frntc/Sidekick64/Source/Firmware/kernel_sid.cpp

/*
  _________.__    .___      __   .__        __          _________.___________   
 /   _____/|__| __| _/____ |  | _|__| ____ |  | __     /   _____/|   \______ \  
 \_____  \ |  |/ __ |/ __ \|  |/ /  |/ ___\|  |/ /     \_____  \ |   ||    |  \ 
 /        \|  / /_/ \  ___/|    <|  \  \___|    <      /        \|   ||    `   \
/_______  /|__\____ |\___  >__|_ \__|\___  >__|_ \    /_______  /|___/_______  /
        \/         \/    \/     \/       \/     \/            \/             \/ 
 
 kernel_sid.cpp

 Sidekick64 - A framework for interfacing 8-Bit Commodore computers (C64/C128,C16/Plus4,VC20) and a Raspberry Pi Zero 2 or 3A+/3B+
            - Sidekick SID: a SID and SFX Sound Expander Emulation 
  		      (using reSID by Dag Lem and FMOPL by Jarek Burczynski, Tatsuyuki Satoh, Marco van den Heuvel, and Acho A. Tang)
 Copyright (c) 2019-2022 Carsten Dachsbacher <frenetic@dachsbacher.de>

 Logo created with http://patorjk.com/software/taag/
 
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
 You should have received a copy of the GNU General Public License
 along with this program.  If not, see <http://www.gnu.org/licenses/>.
*/
#include <math.h>
#include "kernel_sid.h"
#ifdef COMPILE_MENU
#include "kernel_menu.h"
#include "launch.h"

static u32 launchPrg;
#endif


//static const char FILENAME_MIDI_SOUNDFONT[] = "SD:MIDI/TimGM6mb.sf2";	// 6 mb
//static const char FILENAME_MIDI_SOUNDFONT[] = "SD:MIDI/Ct4mgm.sf2";	// 4 mb
//static const char FILENAME_MIDI_SOUNDFONT[] = "SD:MIDI/FluidR3_GM.sf2";

static const char FILENAME_SPLASH_RGB[] = "SD:SPLASH/sk64_sid_bg2.tga";
static const char FILENAME_SPLASH_RGB2[] = "SD:SPLASH/sk64_sid_bg.tga";
static const char FILENAME_LED_RGB[] = "SD:SPLASH/sk64_sid_led.tga";

//                 _________.___________         ____                      ________    ______  ____________  
//_______   ____  /   _____/|   \______ \       /  _ \       ___.__. _____ \_____  \  /  __  \/_   \_____  \ 
//\_  __ \_/ __ \ \_____  \ |   ||    |  \      >  _ </\    <   |  |/     \  _(__  <  >      < |   |/  ____/ 
// |  | \/\  ___/ /        \|   ||    `   \    /  <_\ \/     \___  |  Y Y  \/       \/   --   \|   /       \ 
// |__|    \___  >_______  /|___/_______  /    \_____\ \     / ____|__|_|  /______  /\______  /|___\_______ \
//             \/        \/             \/            \/     \/          \/       \/        \/             \/
#include "resid/sid.h"

using namespace reSID;
u32 CLOCKFREQ = 985248;	// exact clock frequency of the C64 will be measured at start up

// SID types and digi boost (only for MOS8580)
unsigned int SID_MODEL[2] = { 8580, 8580 };
unsigned int SID_DigiBoost[2] = { 0, 0 };

// do not change this value
#define NUM_SIDS 2 
SID *sid[ NUM_SIDS ];

#ifdef EMULATE_OPL2
FM_OPL *pOPL;
u32 fmOutRegister;
u16 hack_OPL_Sample_Value[ 2 ];
u8 hack_OPL_Sample_Enabled;
#endif

extern u8 *flash_cacheoptimized_pool;

// a ring buffer storing SID-register writes (filled in FIQ handler)
// TODO should be much smaller
#define RING_SIZE (1024*80)
static u32 *ringBufGPIO;// = (u32*)&flash_cacheoptimized_pool[ 0 ]; //[ RING_SIZE ];
static unsigned long long *ringTime;// = (unsigned long long *)&flash_cacheoptimized_pool[ RING_SIZE * 4 ]; //[ RING_SIZE ];
//static u32 ringBufGPIO[ RING_SIZE ];
//static unsigned long long ringTime[ RING_SIZE ];
static u32 ringWrite;

// prepared GPIO output when SID-registers are read
u32 outRegisters[ 32 ];
u32 outRegisters_2[ 32 ];

u32 fmFakeOutput = 0;
u32 fmAutoDetectStep = 0;
u32 sidFakeOutput = 0;
u32 sidAutoDetectStep = 0;
u32 sidAutoDetectStep_2 = 0;
uint8_t sidAutoDetectRegs[ 32 ];
uint8_t sidAutoDetectRegs_2[ 32 ];

// counts the #cycles when the C64-reset line is pulled down (to detect a reset)
u32 resetCounter,
	cyclesSinceReset,  
	resetPressed, resetReleased;

// Datel MIDI-interface
/*const uint8_t MIDI_CONTROL_REG  = 0x04;
const uint8_t MIDI_STATUS_REG   = 0x06;
const uint8_t MIDI_TRANSMIT_REG = 0x05;
const uint8_t MIDI_RECEIVE_REG  = 0x07;*/

// Sequential MIDI-interface
const uint8_t MIDI_CONTROL_REG  = 0x00;
const uint8_t MIDI_STATUS_REG   = 0x02;
const uint8_t MIDI_TRANSMIT_REG = 0x01;
const uint8_t MIDI_RECEIVE_REG  = 0x03;

// Passport/Sentech MIDI-interface
/*const uint8_t MIDI_CONTROL_REG  = 0x08;
const uint8_t MIDI_STATUS_REG   = 0x08;
const uint8_t MIDI_TRANSMIT_REG = 0x09;
const uint8_t MIDI_RECEIVE_REG  = 0x09;*/

// Datel + Sequential simultaneously
// => address < 8 and (address&3)==sequential

#define SUPPORT_MIDI

#ifdef SUPPORT_MIDI

#define TSF_IMPLEMENTATION
#define TSF_NO_STDIO
#include "tsf.h"

tsf *TinySoundFont = NULL;
#endif

// this is the actual configuration of the emulation
u32 cfgRegisterRead = 0;			// don't use this when you have a SID(-replacement) in the C64
u32 cfgEmulateOPL2 = 1;
u32 cfgSID2_Disabled = 0;
u32 cfgSID2_PlaySameAsSID1 = 0;
u32 cfgMixStereo = 1;
u32 cfgSID2_Addr = 0;
s32 cfgVolSID1_Left, cfgVolSID1_Right;
s32 cfgVolSID2_Left, cfgVolSID2_Right;
s32 cfgVolOPL_Left, cfgVolOPL_Right;
s32 cfgMIDI = 0, cfgSoundFont = 0, cfgMIDIVolume = 0;

extern u32 wireSIDAvailable;

u32 outputPWM = 1, outputHDMI = 0, outputHDMISound = 0;

void setSIDConfiguration( u32 mode, u32 sid1, u32 sid2, u32 sid2addr, u32 rr, u32 addr, u32 exp, s32 v1, s32 p1, s32 v2, s32 p2, s32 v3, s32 p3, s32 outputPWMHDMI, s32 MIDI, s32 soundfont, s32 midiVol )
{
	SID_MODEL[ 0 ] = ( sid1 == 0 ) ? 6581 : 8580;
	SID_DigiBoost[ 0 ] = ( sid1 == 2 ) ? 1 : 0;
	SID_MODEL[ 1 ] = ( sid2 == 0 ) ? 6581 : 8580;
	SID_DigiBoost[ 1 ] = ( sid2 == 2 ) ? 1 : 0;

	// panning = 0 .. 14, vol = 0 .. 15
	// volumes -> 0 .. 255
	cfgVolSID1_Left  = v1 * ( 14 - p1 );
	cfgVolSID1_Right = v1 * ( p1 );
	cfgVolSID2_Left  = v2 * ( 14 - p2 );
	cfgVolSID2_Right = v2 * ( p2 );
	cfgVolOPL_Left  = v3 * ( 14 - p3 );
	cfgVolOPL_Right = v3 * ( p3 );

	if ( outputPWMHDMI == 0 || outputPWMHDMI == 2 )
	{
		int maxVolFactor = max( cfgVolSID1_Left, max( cfgVolSID1_Right, max( cfgVolSID2_Left, max( cfgVolSID2_Right, max( cfgVolOPL_Left, cfgVolOPL_Right ) ) ) ) );

		cfgVolSID1_Left  = cfgVolSID1_Left  * 256 / maxVolFactor;
		cfgVolSID1_Right = cfgVolSID1_Right * 256 / maxVolFactor;
		cfgVolSID2_Left  = cfgVolSID2_Left  * 256 / maxVolFactor;
		cfgVolSID2_Right = cfgVolSID2_Right * 256 / maxVolFactor;
		cfgVolOPL_Left   = cfgVolOPL_Left   * 256 / maxVolFactor;
		cfgVolOPL_Right  = cfgVolOPL_Right  * 256 / maxVolFactor;
	}

	if ( sid2 == 3 ) 
	{ 
		cfgSID2_Disabled = 1; cfgVolSID2_Left = cfgVolSID2_Right = 0;
	} else 
		cfgSID2_Disabled = 0;

	if ( addr == 0 ) cfgSID2_PlaySameAsSID1 = 1; else cfgSID2_PlaySameAsSID1 = 0;
	if ( mode == 0 ) cfgMixStereo = 1; else cfgMixStereo = 0;


	cfgSID2_Addr = sid2addr; // 0 = $d420, 1 = $d500, 2 = $de00
	cfgRegisterRead = rr;
	cfgEmulateOPL2 = exp;

	/*if ( !wireSIDAvailable )
	{
		cfgVolSID1_Left  = 0;
		cfgVolSID1_Right = 0;
		cfgVolSID2_Left  = 0;
		cfgVolSID2_Right = 0;
		cfgSID2_Disabled = 0;
		cfgRegisterRead  = 0;
	}*/

	if ( !exp )
	{
		cfgVolOPL_Left = cfgVolOPL_Right = 0;
	}

	outputPWM = outputHDMI = outputHDMISound = 0;
	#ifdef USE_PWM_DIRECT
	if ( outputPWMHDMI == 0 || outputPWMHDMI == 2 )
		outputPWM = 1;
	#endif
	#ifdef HDMI_SOUND
	if ( outputPWMHDMI == 1 || outputPWMHDMI == 2 )
		outputHDMISound = 1;
	#endif

	cfgMIDI = MIDI;
	cfgSoundFont = soundfont;
	cfgMIDIVolume = midiVol;
}

//  __     __                __      ___                   ___ 
// /__` | |  \     /\  |\ | |  \    |__   |\/|    | |\ | |  |  
// .__/ | |__/    /~~\ | \| |__/    |     |  |    | | \| |  |  
//                                                            
void initSID()
{
	resetCounter = 0;

	for ( int i = 0; i < NUM_SIDS; i++ )
	{
		sid[ i ] = new SID;

		for ( int j = 0; j < 25; j++ )
			sid[ i ]->write( j, 0 );

		if ( SID_MODEL[ i ] == 6581 )
		{
			sid[ i ]->set_chip_model( MOS6581 );
			sid[ i ]->set_voice_mask( 0x07 );
			sid[ i ]->input( 0 );
		} else
		{
			sid[ i ]->set_chip_model( MOS8580 );
			if ( SID_DigiBoost[ i ] == 0 )
			{
				sid[ i ]->set_voice_mask( 0x07 );
				sid[ i ]->input( 0 );
			} else
			{
				sid[ i ]->set_voice_mask( 0x0f );
				sid[ i ]->input( -8192 );
			}
		}

		int SID_passband = 90;
		int SID_gain = 97;
		int SID_filterbias = 1000;

		sid[ i ]->adjust_filter_bias( SID_filterbias / 1000.0f );
		sid[ i ]->set_sampling_parameters( CLOCKFREQ, SAMPLE_FAST, SAMPLERATE, SAMPLERATE * SID_passband / 200.0f, SID_gain / 100.0f );
	}

#ifdef EMULATE_OPL2
	if ( cfgEmulateOPL2 )
	{
		pOPL = ym3812_init( 3579545, SAMPLERATE );
		ym3812_reset_chip( pOPL );
		hack_OPL_Sample_Value[ 0 ] = hack_OPL_Sample_Value[ 1 ] = 0;
		hack_OPL_Sample_Enabled = 0;
		fmFakeOutput = 0;
	}
#endif
	fmFakeOutput =
	fmAutoDetectStep = 0;

	sidFakeOutput =
	sidAutoDetectStep =
	sidAutoDetectStep_2 = 0;

	for ( int i = 0; i < 32; i++ )
		outRegisters[ i ] = outRegisters_2[ i ] = 0;

	outRegisters[ 25 ] = outRegisters_2[ 25 ] = 255;
	outRegisters[ 26 ] = outRegisters_2[ 26 ] = 255;

	for ( int i = 0; i < 20; i++ )
	{
		sidAutoDetectRegs[ i ] = 0;
		sidAutoDetectRegs_2[ i ] = 0;
	}

	// ring buffer init
	ringWrite = 0;
	for ( int i = 0; i < RING_SIZE; i++ )
		ringTime[ i ] = 0;
}


unsigned long long cycleCountC64;


#ifdef COMPILE_MENU
extern CLogger			*logger;
extern CTimer			*pTimer;
extern CScheduler		*pScheduler;
extern CInterruptSystem	*pInterrupt;
extern CScreenDevice	*screen;
CSoundBaseDevice	*m_pSound = NULL;
#else

CLogger				*logger;
CTimer				*pTimer;
CScheduler			*pScheduler;
CInterruptSystem	*pInterrupt;
CScreenDevice		*screen;


boolean CKernel::Initialize( void )
{
	boolean bOK = TRUE;

#ifdef USE_HDMI_VIDEO
	if ( bOK ) bOK = m_Screen.Initialize();

	if ( bOK )
	{
		CDevice *pTarget = m_DeviceNameService.GetDevice( m_Options.GetLogDevice(), FALSE );
		if ( pTarget == 0 )
			pTarget = &m_Screen;

		bOK = m_Logger.Initialize( pTarget );
		logger = &m_Logger;
	}
#endif

	if ( bOK ) bOK = m_Interrupt.Initialize();
	if ( bOK ) bOK = m_Timer.Initialize();


	pTimer = &m_Timer;
	pScheduler = &m_Scheduler;
	pInterrupt = &m_Interrupt;
	screen = &m_Screen;

	return bOK;
}
#endif

void quitSID()
{
	for ( int i = 0; i < NUM_SIDS; i++ )
		delete sid[ i ];

#ifdef SUPPORT_MIDI
	if ( TinySoundFont )
		tsf_close( TinySoundFont );
#endif
}

static u32 renderDone = 0;

static u32 visMode = 0;
static u32 visModeGotoNext = 0;

static float px = 120.0f;
static float dx = 0.0f;
static s32 startRow = 1, endRow = 1;
static float vuValueAvg = 0.01f;
static u32 visUpdate = 1;
static int scopeX = 0;
static u8 scopeValues[ 240 ] = {0};
static u32 nPrevLEDs[3] = {0, 0, 0};
static float ledValueAvg[3] = { 0.01f, 0.01f, 0.01f };

static void initVisualization()
{
	visMode = 0;
	visModeGotoNext = 0;
	px = 120.0f;
	dx = 0.0f;
	startRow = 1; endRow = 1;
	vuValueAvg = 0.01f;
	visUpdate = 1;
	scopeX = 0;
	memset( scopeValues, 0, 256 );
	nPrevLEDs[0] = nPrevLEDs[1] = nPrevLEDs[2] = 0;
	ledValueAvg[0] = ledValueAvg[1] = ledValueAvg[2] = 0.01f;
}

static unsigned char tftBackground2[ 240 * 240 * 2 ];
static unsigned char tftLEDs[ 240 * 240 * 2 ];

static u32 vu_Mode = 0;
static u32 vuMeter[4] = { 0, 0, 0, 0 };
static u32 vu_nLEDs = 0xffff;

static u32 allUsedLEDs = 0;

static int busValue = 0;
static int busValueTTL = 0;
static unsigned long long nCyclesEmulated = 0;
static unsigned long long samplesElapsed = 0;

static u32 resetFromCodeState = 0;
static u32 _playingPSID = 0;

static u32 nBytesRead, stage;


static void prepareOnReset( bool refresh = false )
{
#ifdef SUPPORT_MIDI
	if ( TinySoundFont )
		tsf_reset( TinySoundFont );
#endif

	fmFakeOutput =
	fmAutoDetectStep = 0;

	sidFakeOutput =
	sidAutoDetectStep =
	sidAutoDetectStep_2 = 0;

	for ( int i = 0; i < 20; i++ )
	{
		sidAutoDetectRegs[ i ] = 0;
		sidAutoDetectRegs_2[ i ] = 0;
	}

	if ( launchPrg )
		{disableCart = 0; SETCLR_GPIO( configGAMEEXROMSet | bNMI, configGAMEEXROMClr );} else
		{SETCLR_GPIO( bNMI | bDMA | bGAME | bEXROM, 0 );}

	if ( !refresh )
	{
		CleanDataCache();
		InvalidateDataCache();
		InvalidateInstructionCache();
	}

	for ( u32 i = 0; i < 4; i++ )
	{
		if ( _playingPSID )
		{
			extern unsigned char charset[ 4096 ];
			CACHE_PRELOAD_DATA_CACHE( &charset[ 2048 ], 1024, CACHE_PRELOADL2KEEP );
			FORCE_READ_LINEAR32a( (void*)&charset[ 2048 ], 1024, 8192 );
		}

		if ( launchPrg )
		{
			launchPrepareAndWarmCache();
		}

		// FIQ handler
		CACHE_PRELOAD_INSTRUCTION_CACHE( (void*)&FIQ_HANDLER, 6*1024 );
		FORCE_READ_LINEAR32a( (void*)&FIQ_HANDLER, 6*1024, 32768 );
	}

	resetCounter = cycleCountC64 = nCyclesEmulated = samplesElapsed = 0;
	nBytesRead = 0; stage = 1;
}

//static u32 haltC64 = 0, letgoC64 = 0;
//static u32 SID_not_initialized = 1;


u32 SAMPLERATE_ADJUSTED = SAMPLERATE;
extern u32 nSamplesPrecompute;
u32 trackSampleProgress;


u32 fillSoundBuffer;

#ifdef SUPPORT_MIDI

#define MIDI_BUF_SIZE_BITS	5
const int midiBufferSize = 1 << MIDI_BUF_SIZE_BITS;
static float midiSampleBuffer[ 1 << (MIDI_BUF_SIZE_BITS) ] AAA;
static u32 midiBufferOfs = midiBufferSize;

#endif

static int first = 1;


#ifdef COMPILE_MENU
void KernelSIDFIQHandler( void *pParam );

void KernelSIDRun( CGPIOPinFIQ m_InputPin, CKernelMenu *kernelMenu, const char *FILENAME, bool hasData = false, u8 *prgDataExt = NULL, u32 prgSizeExt = 0, u32 c128PRG = 0, u32 playingPSID = 0 )
#else
void CKernel::Run( void )
#endif
{
startHereAfterReset:
	// initialize ARM cycle counters (for accurate timing)
	initCycleCounter();

	// initialize GPIOs
	gpioInit();
	SET_BANK2_OUTPUT

	// initialize latch and software I2C buffer
	initLatch();

	#ifndef COMPILE_MENU
	int screenType = 0;
	#endif

	if ( screenType == 0 )
		allUsedLEDs = LATCH_LED_ALL;
	if ( screenType == 1 )
		allUsedLEDs = LATCH_LED0to1;
	
	latchSetClearImm( 0, LATCH_RESET | allUsedLEDs | LATCH_ENABLE_KERNAL );
	latchSetClear( 0, LATCH_RESET | allUsedLEDs | LATCH_ENABLE_KERNAL );

	SETCLR_GPIO( bNMI | bDMA | bGAME | bEXROM, 0 );

	#ifdef COMPILE_MENU
	_playingPSID = playingPSID;

	if ( screenType == 0 )
	{
		splashScreen( raspi_sid_splash );
	} else
	if ( screenType == 1 )
	{
		tftLoadBackgroundTGA( DRIVE, FILENAME_SPLASH_RGB, 8 );

		int w, h; 
		extern char FILENAME_LOGO_RGBA[128];
		extern unsigned char tempTGA[ 256 * 256 * 4 ];

		if ( tftLoadTGA( DRIVE, FILENAME_LOGO_RGBA, tempTGA, &w, &h, true ) )
		{
			tftBlendRGBA( tempTGA, tftBackground, 0 );
		}

		tftCopyBackground2Framebuffer();

		u32 c1 = rgb24to16( 166, 250, 128 );
		u32 c2 = rgb24to16( 98, 216, 204 );
		u32 c3 = rgb24to16( 233, 114, 36 );
		char b1[64], b2[64], b3[64];
		int charWidth = 16;
		const char *addr[3] = { "$d420", "$d500", "$de00" };

		sprintf( b1, "%s", SID_MODEL[ 0 ] == 6581 ? "6581":"8580" );

		if ( cfgSID2_Disabled )
			b2[ 0 ] = 0; else
		{
			if ( cfgSID2_PlaySameAsSID1 )
			sprintf( b2, "+%s/$d400", SID_MODEL[ 1 ] == 6581 ? "6581":"8580"); else
			sprintf( b2, "+%s/%s", SID_MODEL[ 1 ] == 6581 ? "6581":"8580", addr[cfgSID2_Addr]);
		}

		if ( cfgEmulateOPL2 )
			sprintf( b3, "+fm" ); else
			b3[ 0 ] = 0;

		int l = strlen( b1 ) + strlen( b2 ) + strlen( b3 );
		if ( l * 16 >= 240 )
			charWidth = 13;
		int sx = max( 0, ( 240 - charWidth * l ) / 2 - 2 );
		tftPrint( b1, sx, 224, c1, charWidth == 16 ? 0 : -3 );	sx += strlen( b1 ) * charWidth;
		tftPrint( b2, sx, 224, c2, charWidth == 16 ? 0 : -3 );	sx += strlen( b2 ) * charWidth;
		tftPrint( b3, sx, 224, c3, charWidth == 16 ? 0 : -3 );

#ifdef SUPPORT_MIDI
		if ( cfgMIDI )
		{
						//01234567890123456789
			sprintf( b1, "midi/$de0X" );
			sx = max( 0, ( 240 - charWidth * 10 ) / 2 - 2 );
			tftPrint( b1, sx, 224-16, c1, charWidth == 16 ? 0 : -3 );	
		}
#endif

		tftInit();
		tftSendFramebuffer16BitImm( tftFrameBuffer );
		tftConvertFrameBuffer12Bit();

		tftClearDirty();
		extern void tftPrepareDirtyUpdates();
		tftPrepareDirtyUpdates();
		tftUse12BitColor();

		memcpy( tftBackground2, tftBackground, 240 * 240 * 2 );
		tftLoadBackgroundTGA( DRIVE, FILENAME_LED_RGB, 8 );
		memcpy( tftLEDs, tftBackground, 240 * 240 * 2 );

		tftLoadBackgroundTGA( DRIVE, FILENAME_SPLASH_RGB2, 8 );

		initVisualization();
	} 
	#endif

	ringBufGPIO = (u32*)&flash_cacheoptimized_pool[ 0 ];
	ringTime = (unsigned long long *)&flash_cacheoptimized_pool[ RING_SIZE * 4 ]; 

	//
	// MIDI
	//
#ifdef SUPPORT_MIDI
	if ( cfgMIDI )
	{
		u32 size;
		cfgMIDI = 0;
		char filename[256];
		sprintf( filename, "SD:MIDI/instrument%02d.sf2", cfgSoundFont );
		if ( getFileSize( logger, DRIVE, filename, &size ) )
		{
			if ( size < 256 * 1024 * 1024 )
			{
				u8 *soundfont = new u8[ size ];

				if ( readFile( logger, DRIVE, filename, soundfont, &size ) )
				{
					TinySoundFont = tsf_load_memory( soundfont, size );
					tsf_set_output( TinySoundFont, TSF_MONO, SAMPLERATE, 0.0f );
					//tsf_set_output( TinySoundFont, TSF_STEREO_INTERLEAVED, SAMPLERATE, 0.0f );
					tsf_set_volume( TinySoundFont, 0.5f * (float)cfgMIDIVolume / 15.0f );
					tsf_set_max_voices( TinySoundFont, 64 );
					tsf_channel_set_bank_preset( TinySoundFont, 9, 128, 0 );
					cfgMIDI = 1;
				}
				delete [] soundfont;

				memset( midiSampleBuffer, 0, midiBufferSize * sizeof( float ) );
			}
		}
	}
#endif

	//
	// initialize sound output (either PWM which is output in the FIQ handler, or via HDMI)
	//
	logger->Write( "", LogNotice, "initialize sound output..." );
	initSoundOutput( &m_pSound, NULL, outputPWM | outputHDMISound, outputHDMI );

	#ifdef COMPILE_MENU
	disableCart = 0;

	if ( FILENAME == NULL && !hasData )
	{
		SETCLR_GPIO( bNMI | bDMA | bGAME | bEXROM, 0 );
		launchPrg = 0;
		disableCart = 1;
	} else
	{
		SETCLR_GPIO( configGAMEEXROMSet | bNMI, configGAMEEXROMClr );
		launchPrg = 1;
		if ( launchGetProgram( FILENAME, hasData, prgDataExt, prgSizeExt ) )
			launchInitLoader( false, c128PRG ); else
			launchPrg = 0;
	}
	#endif

	logger->Write( "", LogNotice, "initialize SIDs..." );
	initSID();
	logger->Write( "", LogNotice, "bla..." );

	// ring buffer init
	ringWrite = 0;
	for ( int i = 0; i < RING_SIZE; i++ )
		ringTime[ i ] = 0;

	//
	// setup FIQ
	//
	resetReleased = 0xff;
	resetFromCodeState = 0;

	logger->Write( "", LogNotice, "setup fiq..." );

	#ifdef COMPILE_MENU
	prepareOnReset();
	m_InputPin.ConnectInterrupt( KernelSIDFIQHandler, kernelMenu );
	#else
	m_InputPin.ConnectInterrupt( this->FIQHandler, this );
	#endif
	m_InputPin.EnableInterrupt( GPIOInterruptOnRisingEdge );

	logger->Write( "", LogNotice, "start emulating..." );
	cycleCountC64 = 0;
	nCyclesEmulated = 0;
	samplesElapsed = 0;

	// how far did we consume the commands in the ring buffer?
	unsigned int ringRead = 0;

	#ifdef COMPILE_MENU
	prepareOnReset( true );
	DELAY(1<<22);
	prepareOnReset( true );
	DELAY(1<<22);
	//startHereAfterReset2:
	cycleCountC64 = 0;
	resetCounter = 0;
	latchSetClear( LATCH_RESET, allUsedLEDs | LATCH_ENABLE_KERNAL );

	nBytesRead = 0; stage = 1;
	u32 cycleCountC64_Stage1 = 0;

	first = 1;
	#ifdef HDMI_SOUND
	//extern CHDMISoundBaseDevice *hdmiSoundDevice;
	//hdmiSoundDevice->Cancel();
	//hdmiSoundDevice->Start();
	#endif

	latchSetClear( LATCH_RESET, 0 );
	if ( launchPrg )
	{
		while ( !disableCart )
		{
			if ( ( ( stage == 1 ) && nBytesRead > 0 ) ||
 				 ( ( stage == 2 ) && nBytesRead < 32 && cycleCountC64 - cycleCountC64_Stage1 > 500000 ) )
			{
				if ( stage == 1 ) 
				{ 
					stage = 2; cycleCountC64_Stage1 = cycleCountC64; 
				} else 
				{
					stage = 0;
					latchSetClear( 0, LATCH_RESET );
					DELAY(1<<20);
					latchSetClear( LATCH_RESET, 0 );
					nBytesRead = 0; stage = 1;
					cycleCountC64 = 0;
				}
			}
		
			#ifdef COMPILE_MENU
			TEST_FOR_JUMP_TO_MAINMENU( cycleCountC64, resetCounter )
			#endif
			asm volatile ("wfi");

			if ( resetFromCodeState == 2 )
			{
				EnableIRQs();
				m_InputPin.DisableInterrupt();
				m_InputPin.DisconnectInterrupt();
				return;		
			}
			
/*			if ( cycleCountC64 > 2000000 )
			{
				cycleCountC64 = 0;
				latchSetClear( 0, LATCH_RESET );
				DELAY(1<<20);
				latchSetClear( LATCH_RESET, 0 );
			}*/
		}
		//latchSetClearImm( LATCH_LED0, 0 );
		if ( _playingPSID )
		{
			extern unsigned char charset[ 4096 ];
			CACHE_PRELOAD_DATA_CACHE( &charset[ 2048 ], 1024, CACHE_PRELOADL2KEEP );
		}
		DELAY(1<<22);
	} 
	#endif

	resetReleased = 0;
	resetCounter = cycleCountC64 = 0;
	nCyclesEmulated = 0;
	samplesElapsed = 0;
	ringRead = ringWrite = 0;

	static u32 hdmiVol = 1;

	fillSoundBuffer = 0;

	// mainloop
	while ( true )
	{
		#ifdef COMPILE_MENU
		//TEST_FOR_JUMP_TO_MAINMENU( cycleCountC64, resetCounter )
		if ( cycleCountC64 > 2000000 && resetCounter > 0 && outputHDMI && m_pSound && hdmiVol == 1 ) {
			#ifdef HDMI_SOUND
			//hdmiSoundDevice->Cancel();
			#endif

			hdmiVol = 0;
		}
		if ( cycleCountC64 > 2000000 && resetCounter > 500000 ) {
			//logger->Write( "", LogNotice, "adjusted sample rate: %u Hz", (u32)SAMPLERATE_ADJUSTED );
			#ifdef HDMI_SOUND
			/*extern CHDMISoundBaseDevice *hdmiSoundDevice;
			if ( outputHDMISound )
				hdmiSoundDevice->Cancel();*/
			#endif
			quitSID();
			EnableIRQs();
			m_InputPin.DisableInterrupt();
			m_InputPin.DisconnectInterrupt();
			return;
		}
		#endif

		if ( resetReleased == 1 )
		{
			//logger->Write( "", LogNotice, "adjusted sample rate: %u Hz", (u32)SAMPLERATE_ADJUSTED );
			quitSID();

			EnableIRQs();
			m_InputPin.DisableInterrupt();
			m_InputPin.DisconnectInterrupt();
			goto startHereAfterReset;
		}

		#ifdef COMPILE_MENU
		//if ( screenType_ == 0 )
		{
			if ( renderDone == 2 )
			{
				if ( !sendFramebufferDone() )
					sendFramebufferNext( 1 );		

				if ( sendFramebufferDone() )
					renderDone = 3;
			}
			if ( bufferEmptyI2C() && renderDone == 1 )
			{
				sendFramebufferStart();
				renderDone = 2;
			}
		}
		#endif

	#ifndef EMULATION_IN_FIQ

		s16 val1, val2;
		s32 valOPL;

		unsigned long long cycleCount = cycleCountC64;
		while ( cycleCount > nCyclesEmulated + 20 ) // TODO should be > nCyclesEmulated + 985240/48000
		{
			CACHE_PRELOAD_INSTRUCTION_CACHE( (void*)&FIQ_HANDLER, 6*1024 );

			CACHE_PRELOADL2STRMW( &smpCur );

			unsigned long long samplesElapsedBefore = samplesElapsed;

			long long cycleNextSampleReady = ( ( unsigned long long )(samplesElapsedBefore+1) * ( unsigned long long )CLOCKFREQ ) / ( unsigned long long )SAMPLERATE_ADJUSTED;
			u32 cyclesToNextSample = cycleNextSampleReady - nCyclesEmulated;

			do { // do SID emulation until time passed to create an additional sample (i.e. there may be several cycles until a sample value is created)
				//u32 cyclesToEmulate = min( 256, cycleCount - nCyclesEmulated );
				u32 cyclesToEmulate = min( 32, cycleCount - nCyclesEmulated );

				if ( cyclesToEmulate > cyclesToNextSample )
					cyclesToEmulate = cyclesToNextSample;

				if ( ringRead != ringWrite )
				{
					int cyclesToNextWrite = (signed long long)ringTime[ ringRead ] - (signed long long)nCyclesEmulated;

					if ( (int)cyclesToEmulate > cyclesToNextWrite && cyclesToNextWrite > 0 )
						cyclesToEmulate = cyclesToNextWrite;
				}
				if ( cyclesToEmulate <= 0 )
					cyclesToEmulate = 1;

				//if ( cyclesToEmulate > 0 )
				{
					sid[ 0 ]->clock( cyclesToEmulate );
					#ifndef SID2_DISABLED
					if ( !cfgSID2_Disabled )
						sid[ 1 ]->clock( cyclesToEmulate );
					#endif

					outRegisters[ 27 ] = sid[ 0 ]->read( 27 );
					outRegisters[ 28 ] = sid[ 0 ]->read( 28 );
					if ( !cfgSID2_Disabled )
					{
						outRegisters_2[ 27 ] = 0;
						outRegisters_2[ 28 ] = 0;
					}

					nCyclesEmulated += cyclesToEmulate;
					cyclesToNextSample -= cyclesToEmulate;
				}


				// apply register updates (we do one-cycle emulation steps, but in case we need to catch up...)
				unsigned int readUpTo = ringWrite;

				if ( ringRead != readUpTo && nCyclesEmulated >= ringTime[ ringRead ] )
				{
      quicklyGetAnotherRegisterWrite:
#ifdef SUPPORT_MIDI
					if ( cfgMIDI && (ringBufGPIO[ ringRead ] & (1<<31)) ) // MIDI
					{
						register u8 MC = ringBufGPIO[ ringRead ] & 255;
						register u8 MD1 = ( ringBufGPIO[ ringRead ] >> 8 ) & 255;
						register u8 MD2 = ( ringBufGPIO[ ringRead ] >> 16 ) & 255;
						register u16 pitch;

						register u8 channel = MC & 0x0f;
						MC &= 0xf0;

						switch ( MC )
						{
						default:
							break;
						case 0x90: // note on
							tsf_channel_note_on( TinySoundFont, channel, MD1, (float)MD2 / 127.0f ); 
							break;
						case 0x80: // note off
							tsf_channel_note_off( TinySoundFont, channel, MD1 ); 
							break;
						case 0xc0: // program change
							tsf_channel_set_presetnumber( TinySoundFont, channel, MD1, ( channel == 9 ) );
							break;
						/*case 0xd0: // pressure change
							break;*/
						case 0xe0: // pitch bend
							pitch = MD1 | ( MD2 << 7 );
							tsf_channel_set_pitchwheel( TinySoundFont, channel, pitch );
							break;
						case 0xb0: // control change
							tsf_channel_midi_control( TinySoundFont, channel, MD1, MD2 );
							break;
						}		
					} else
#endif
					{

						unsigned char A, D;
						decodeGPIO( ringBufGPIO[ ringRead ], &A, &D );

						#ifdef EMULATE_OPL2
						if ( cfgEmulateOPL2 && (ringBufGPIO[ ringRead ] & bIO2) )
						{
							if ( ( ( A & ( 1 << 4 ) ) == 0 ) )
							{
								ym3812_write( pOPL, 0, D ); 
							} else
							{
								ym3812_write( pOPL, 1, D );
								if ( pOPL->address == 1 )
								{
									if ( D == 4 ) // enable digi hack
										hack_OPL_Sample_Enabled = 1;  else
										hack_OPL_Sample_Enabled = 0;
								}
								if ( hack_OPL_Sample_Enabled && ( pOPL->address == 0xa0 || pOPL->address == 0xa1 ) ) // digi hack
									hack_OPL_Sample_Value[ pOPL->address - 0xa0 ] = D; else
									hack_OPL_Sample_Value[ 0 ] = hack_OPL_Sample_Value[ 1 ] = 0;
							}
						} else
						#endif
						//#if !defined(SID2_DISABLED) && !defined(SID2_PLAY_SAME_AS_SID1)
						// TODO: generic masks
						if ( !cfgSID2_Disabled && !cfgSID2_PlaySameAsSID1 && (ringBufGPIO[ ringRead ] & SID2_MASK) )
						{
							sid[ 1 ]->write( A & 31, D );
						} else
						//#endif
						{
							sid[ 0 ]->write( A & 31, D );
							//outRegisters[ A & 31 ] = D;
							//#if !defined(SID2_DISABLED) && defined(SID2_PLAY_SAME_AS_SID1)
							if ( !cfgSID2_Disabled && cfgSID2_PlaySameAsSID1 )
								sid[ 1 ]->write( A & 31, D );
							//#endif
						}
					}
					ringRead++;
					ringRead &= ( RING_SIZE - 1 );

					if ( ringRead != ringWrite )
					{
					  s32 t = ringTime[ ringRead ] - nCyclesEmulated;
					  if ( t <= 0 )
						goto quicklyGetAnotherRegisterWrite;
					} 
				}


//				samplesElapsed = ( ( unsigned long long )nCyclesEmulated * ( unsigned long long )SAMPLERATE ) / ( unsigned long long )CLOCKFREQ;
				samplesElapsed = ( ( unsigned long long )nCyclesEmulated * ( unsigned long long )SAMPLERATE_ADJUSTED ) / ( unsigned long long )CLOCKFREQ;

				if ( nCyclesEmulated >= cycleCount && samplesElapsed == samplesElapsedBefore )
					goto NoSampleGeneratedYet;

			} while ( samplesElapsed == samplesElapsedBefore );

			CACHE_PRELOADL2STRMW( &sampleBuffer[ smpCur ] );
			val1 = sid[ 0 ]->output();
			val2 = 0;
			valOPL = 0;

		#ifndef SID2_DISABLED
			if ( !cfgSID2_Disabled )
				val2 = sid[ 1 ]->output();
		#endif

		#ifdef EMULATE_OPL2
			if ( cfgEmulateOPL2 )
			{
				ym3812_update_one( pOPL, &valOPL, 1 );
				// TODO asynchronous read back is an issue, needs to be fixed
				fmOutRegister = encodeGPIO( ym3812_read( pOPL, 0 ) ); 
			}

			if ( hack_OPL_Sample_Enabled )
		        valOPL = ( hack_OPL_Sample_Value[ 0 ] << 5 ) + ( hack_OPL_Sample_Value[ 1 ] << 5 );
		#endif

			//
			// mixer
			//
			register s32 left, right;

#ifdef SUPPORT_MIDI
			register s32 midiSampleLeft;

			midiSampleLeft = 0;
			if ( cfgMIDI )
			{
				if ( midiBufferOfs >= midiBufferSize )
				{
					tsf_render_float( TinySoundFont, &midiSampleBuffer[0], midiBufferSize, 0 );
					midiBufferOfs = 0;
				} 

				midiSampleLeft = midiSampleBuffer[ midiBufferOfs ] * 32767.0f;
				midiSampleBuffer[ midiBufferOfs ] = 0.0f;
				midiBufferOfs ++;
				midiSampleLeft = max( -31768+2, min( 31767-2, midiSampleLeft ) );
			}
#endif
			if ( nCyclesEmulated < 400000 )
				val1 = val2 = 0;
			// yes, it's 1 byte shifted in the buffer, need to fix
			right = ( val1 * cfgVolSID1_Left  + val2 * cfgVolSID2_Left  + valOPL * cfgVolOPL_Left ) >> 8;
			left  = ( val1 * cfgVolSID1_Right + val2 * cfgVolSID2_Right + valOPL * cfgVolOPL_Right ) >> 8;

#ifdef SUPPORT_MIDI
			right += midiSampleLeft;
			left  += midiSampleLeft;
#endif

/*			if ( fadeVolume < 65536 ) 
			{
				left = ( left * fadeVolume ) >> 16;
				right = ( right * fadeVolume ) >> 16;
				fadeVolume ++;
			}*/

			right = max( -32768+2, min( 32767-2, right ) );
			left  = max( -32768+2, min( 32767-2, left ) );

			if ( outputPWM ) 
				putSample( left, right );

			if ( outputHDMISound )
				putSampleHDMI( left << 8, right << 8 );

		#if 1
			// vu meter
			static u32 vu_nValues = 0;
			static float vu_Sum[ 4 ] = { 0.0f, 0.0f, 0.0f, 0.0f };
			
			//if ( vu_Mode != 2 )
			{
				float t = (left+right) / (float)32768.0f * 0.5f;
				vu_Sum[ 0 ] += t * t * 1.0f;

				vu_Sum[ 1 ] += val1 * val1 / (float)32768.0f / (float)32768.0f;
				vu_Sum[ 2 ] += val2 * val2 / (float)32768.0f / (float)32768.0f;
				vu_Sum[ 3 ] += valOPL * valOPL / (float)32768.0f / (float)32768.0f;

				if ( ++ vu_nValues == 256*2 )
				{
					for ( u32 i = 0; i < 4; i++ )
					{
						float vu_Volume = max( 0.0f, 2.0f * (log10( 0.1f + sqrt( (float)vu_Sum[ i ] / (float)vu_nValues ) ) + 1.0f) );
						u32 v = vu_Volume * 1024.0f;
						if ( i == 0 )
						{
							// moving average
							float v = min( 1.0f, (float)vuMeter[ 0 ] / 1024.0f );
							static float led4Avg = 0.0f;
							led4Avg = led4Avg * 0.8f + v * ( 1.0f - 0.8f );

							vu_nLEDs = max( 0, min( 4, (led4Avg * 8.0f) ) );
							if ( vu_nLEDs > 4 ) vu_nLEDs = 4;
						}
						vuMeter[ i ] = v;
						vu_Sum[ i ] = 0;
					}

					vu_nValues = 0;
				}
			}

			#ifdef COMPILE_MENU
			if ( screenType == 0 )
			{
				#include "oscilloscope_hack.h"
			} else
			if ( screenType == 1 )
			{
				const float scaleVis = 1.0f;
				const u32 nLevelMeters = 3;
				#include "tft_sid_vis.h"
			} 
			#endif
		#endif
		NoSampleGeneratedYet:;
		}
	#endif
	}

	m_InputPin.DisableInterrupt();
}


// taken from Circle itself for inlining

#define REG(name, base, offset, base4, offset4)	\
			static const u32 Reg##name = (base) + (offset);
#define REGBIT(reg, name, bitnr)	static const u32 Bit##reg##name = 1U << (bitnr);

REG (MaiData, ARM_HD_BASE, 0x20, ARM_HD_BASE, 0x1C);
REG (MaiControl, ARM_HD_BASE, 0x14, ARM_HD_BASE, 0x10);
	REGBIT (MaiControl, Full, 11);

unsigned m_nSubFrame = 0;
	
const u8 IEC958Table[ 5 ] = 
{
	0b100,	// consumer, PCM, no copyright, no pre-emphasis
	0,	// category (general mode)
	0,	// source number, take no account of channel number
	2,	// sampling frequency 48khz
	0b1011 | (13 << 4) // 24 bit samples, original freq.
};

__attribute__( ( always_inline ) ) inline u32 ConvertIEC958Sample( u32 nSample, unsigned nFrame )
{
	nSample &= 0xFFFFFF;
	nSample <<= 4;

	if ( nFrame < IEC958_STATUS_BYTES * 8 && (IEC958Table[nFrame / 8] & BIT(nFrame % 8)) )
		nSample |= 0x40000000;

	if (__builtin_parity(nSample))
		nSample |= 0x80000000;

	if (nFrame == 0)
		nSample |= IEC958_B_FRAME_PREAMBLE;

	return nSample;
}


#ifdef COMPILE_MENU
void KernelSIDLaunchFIQHandler( void *pParam )
{
	if ( !disableCart )
	{
		register u32 D;

		// after this call we have some time (until signals are valid, multiplexers have switched, the RPi can/should read again)
		START_AND_READ_ADDR0to7_RW_RESET_CS

		// update some counters
		UPDATE_COUNTERS_MIN( cycleCountC64, resetCounter )

		// read the rest of the signals
		WAIT_AND_READ_ADDR8to12_ROMLH_IO12_BA

		LAUNCH_FIQ( resetCounter )
	}
}

void KernelSIDFIQHandler( void *pParam )
#else
void CKernel::FIQHandler (void *pParam)
#endif
{
	register u32 D = 0;

	#ifdef COMPILE_MENU
	if ( launchPrg && !disableCart )
	{
		register u32 D;

		CACHE_PRELOADL2STRM( &prgData[ currentOfs ] );

		// after this call we have some time (until signals are valid, multiplexers have switched, the RPi can/should read again)
		START_AND_READ_ADDR0to7_RW_RESET_CS

		// update some counters
		UPDATE_COUNTERS_MIN( cycleCountC64, resetCounter )

		// read the rest of the signals
		WAIT_AND_READ_ADDR8to12_ROMLH_IO12_BA

		if ( CPU_READS_FROM_BUS && ROML_ACCESS )
			nBytesRead++;

		LAUNCH_FIQ( resetCounter )
	}
	#endif
	static s32 latchDelayOut = 10;

	START_AND_READ_ADDR0to7_RW_RESET_CS

	cycleCountC64 ++;

	if ( CPU_RESET && !resetReleased ) {
		resetPressed = 1; resetCounter ++;
	} else {
		if ( resetPressed && resetCounter > 100 )	
		{
			resetReleased = 1;
			disableCart = transferStarted = 0;
			nBytesRead = 0; stage = 1;
			SETCLR_GPIO( configGAMEEXROMSet | bNMI, configGAMEEXROMClr );
			FINISH_BUS_HANDLING
			return;
		}
		resetPressed = 0;
	}

	#ifdef COMPILE_MENU
	// preload cache
	if ( !( launchPrg && !disableCart ) )
	{
		CACHE_PRELOADL1STRMW( &ringWrite );
		CACHE_PRELOADL1STRM( &sampleBuffer[ smpLast ] );
		CACHE_PRELOADL1STRM( &outRegisters[ 16 ] );
	}
	#endif

	WAIT_AND_READ_ADDR8to12_ROMLH_IO12_BA

	if ( busValueTTL < 0 )
	{
		busValue = 0;  
	} else
		busValueTTL --;

	if ( CPU_WRITES_TO_BUS )
		READ_D0to7_FROM_BUS( D )

	//  __   ___       __      __     __  
	// |__) |__   /\  |  \    /__` | |  \ 
	// |  \ |___ /~~\ |__/    .__/ | |__/ 
	//
	if ( cfgRegisterRead && CPU_READS_FROM_BUS && SID_ACCESS )
	{
		u32 A = ( g2 >> A0 );
		u32 D;// = outRegisters[ A ];

		A |= ( (GET_ADDRESS8to12) & 1 ) << 8;

		if ( !cfgSID2_Disabled &&
			 ( ( cfgSID2_Addr == 0 && (A & 0x20) ) || ( cfgSID2_Addr == 1 && (A & 0x100) ) ) )
		{
			A &= 31;
			if ( sidAutoDetectStep_2 == 1 && A == 0x1b )
			{
				sidAutoDetectStep_2 = 0;
				if ( SID_MODEL[ 1 ] == 8580 )
					D = 2; else
					D = 3;
			} else
			{
				if ( A >= 0x19 && A <= 0x1c )
					D = outRegisters_2[ A & 31 ]; else
					D = busValue;
			}
		} else
		{
			A &= 31;
			if ( sidAutoDetectStep == 1 && A == 0x1b )
			{
				sidAutoDetectStep = 0;
				if ( SID_MODEL[ 0 ] == 8580 )
					D = 2; else
					D = 3;
			} else
			{
				if ( A >= 0x19 && A <= 0x1c )
					D = outRegisters[ A ]; else
					D = busValue;
			}
		}

		WRITE_D0to7_TO_BUS( D )

		FINISH_BUS_HANDLING
		return;
	} 
	if ( _playingPSID && IO2_ACCESS )
	{
		if ( CPU_READS_FROM_BUS && GET_IO12_ADDRESS == 0x55 )
		{
			static u32 oc = 0;
			static u8 nextCharByte = 0;
			WRITE_D0to7_TO_BUS( nextCharByte )
			extern unsigned char charset[ 4096 ];
			oc ++; oc &= 1023;
			nextCharByte = charset[ 2048 + oc ];
			FINISH_BUS_HANDLING
			return;
		}
		if ( resetFromCodeState == 0 && CPU_WRITES_TO_BUS && GET_IO12_ADDRESS == 0x11 )
		{
			//READ_D0to7_FROM_BUS( D )
			if ( D == 0x22 )
				resetFromCodeState = 1;
			OUTPUT_LATCH_AND_FINISH_BUS_HANDLING
			return;
		}
		if ( resetFromCodeState == 1 && CPU_WRITES_TO_BUS && GET_IO12_ADDRESS == 0x33 )
		{
			//READ_D0to7_FROM_BUS( D )
			if ( D == 0x44 )
			{
				resetFromCodeState = 2;
				cfgVolSID1_Left = cfgVolSID2_Left = cfgVolOPL_Left =
				cfgVolSID1_Right = cfgVolSID2_Right = cfgVolOPL_Right = 0;
				latchSetClear( 0, LATCH_RESET );
			}
			OUTPUT_LATCH_AND_FINISH_BUS_HANDLING
			return;
		}
	} 
	//  __   ___       __      ___       
	// |__) |__   /\  |  \    |__   |\/| 
	// |  \ |___ /~~\ |__/    |     |  | 
	//                                   
	#ifdef EMULATE_OPL2
	if ( cfgEmulateOPL2 )
	{
		if ( ( CPU_READS_FROM_BUS && IO2_ACCESS ) && ( GET_IO12_ADDRESS == 0x60 ) )
		{
			//
			// this is not a real read of the YM3812 status register!
			// only a fake that let's the detection routine be satisfied
			//
			u32 D = fmFakeOutput; 
			fmFakeOutput = 0xc0 - fmFakeOutput;

			WRITE_D0to7_TO_BUS( D )

			FINISH_BUS_HANDLING
			return;
		} else
		// reading of the external Sound Expander Keyboard => we don't have it, return 0xFF
		if ( ( CPU_READS_FROM_BUS && IO2_ACCESS ) && ( GET_IO12_ADDRESS >= 0x08 ) && ( GET_IO12_ADDRESS <= 0x0F ) )
		{
			WRITE_D0to7_TO_BUS( 0xFF )

			FINISH_BUS_HANDLING
			return;
		} else
		//       __    ___  ___     ___       
		// |  | |__) |  |  |__     |__   |\/| 
		// |/\| |  \ |  |  |___    |     |  | 
		//                                    
		if ( CPU_WRITES_TO_BUS && IO2_ACCESS ) 
		{
			//READ_D0to7_FROM_BUS( D )

			// this is mimicing some behaviour of the YM let it be detected
			u32 A = ( ( g2 & A_FLAG ) >> A0 ) & ( 1 << 4 ); // A == 0 -> address register, otherwise data register
			
			if ( A == 0 && D == 0x04 && fmAutoDetectStep != 2 )
				fmAutoDetectStep = 1;
			if ( A > 0 && D == 0x60 && fmAutoDetectStep == 1 )
				fmAutoDetectStep = 2;
			if ( A == 0 && D == 0x04 && fmAutoDetectStep == 2 )
				fmAutoDetectStep = 3;
			if ( A > 0 && D == 0x80 && fmAutoDetectStep == 3 )
			{
				fmAutoDetectStep = 4;
				fmFakeOutput = 0;
			}
				
			ringBufGPIO[ ringWrite ] = ( g2 & A_FLAG ) | ( D << D0 ) | bIO2;
			ringTime[ ringWrite ] = cycleCountC64;
			ringWrite ++;
			ringWrite &= ( RING_SIZE - 1 );

			FINISH_BUS_HANDLING
			return;
		} 
	} 
	#endif // EMULATE_OPL2
	//       __    ___  ___     __     __  
	// |  | |__) |  |  |__     /__` | |  \ 
	// |/\| |  \ |  |  |___    .__/ | |__/ 
	//                                   
	if ( CPU_WRITES_TO_BUS && SID_ACCESS ) 
	{
		//READ_D0to7_FROM_BUS( D )

		register u32 A = GET_ADDRESS0to7;
		register u32 remapAddr = (A&31) << A0;

		A |= ( (GET_ADDRESS8to12) & 1 ) << 8;

		if ( ( cfgSID2_Addr == 0 && (A & 0x20) ) ||
			 ( cfgSID2_Addr == 1 && (A & 0x100) ) )
		{
			remapAddr |= SID2_MASK;
			if ( sidAutoDetectStep_2 == 0 &&
				 sidAutoDetectRegs_2[ 0x12 ] == 0xff &&
				 sidAutoDetectRegs_2[ 0x0e ] == 0xff &&
				 sidAutoDetectRegs_2[ 0x0f ] == 0xff &&
				 (A&31) == 0x12 && D == 0x20 )
			{
				sidAutoDetectStep_2 = 1;
			}
			sidAutoDetectRegs_2[ A & 31 ] = D;
		} else
		{
			if ( sidAutoDetectStep == 0 &&
				 sidAutoDetectRegs[ 0x12 ] == 0xff &&
				 sidAutoDetectRegs[ 0x0e ] == 0xff &&
				 sidAutoDetectRegs[ 0x0f ] == 0xff &&
				 (A&31) == 0x12 && D == 0x20 )
			{
				sidAutoDetectStep = 1;
			}
			sidAutoDetectRegs[ A & 31 ] = D;
		}


		busValue = D;
		if ( SID_MODEL[ 0 ] == 8580 )
			busValueTTL = 0xa2000; else // 8580
			busValueTTL = 0x1d00; // 6581

		ringBufGPIO[ ringWrite ] = ( remapAddr | ( D << D0 ) ) & ~bIO2;
		ringTime[ ringWrite ] = cycleCountC64;
		ringWrite ++;
		ringWrite &= ( RING_SIZE - 1 );
		
		FINISH_BUS_HANDLING
		return;
	}
	if ( CPU_WRITES_TO_BUS && IO1_ACCESS && cfgSID2_Addr == 2 ) 
	{
		//READ_D0to7_FROM_BUS( D )

		register u32 A = GET_ADDRESS0to7;
		register u32 remapAddr = ( (A&31) << A0 ) | SID2_MASK;

		ringBufGPIO[ ringWrite ] = ( remapAddr | ( D << D0 ) ) & ~bIO2;
		ringTime[ ringWrite ] = cycleCountC64;
		ringWrite ++;
		ringWrite &= ( RING_SIZE - 1 );

		FINISH_BUS_HANDLING
		return;
	}

	// MIDI experimental support
#ifdef SUPPORT_MIDI
	static uint8_t midiFIFO[ 4 ], midiFIFOIdx = 0;
	if ( cfgMIDI && IO1_ACCESS ) 
	{
		register u32 A = GET_ADDRESS0to7;
		register u8 MC, MD1, MD2;

		if ( A < 8 )
		{
			if ( CPU_WRITES_TO_BUS && (A&3) == MIDI_TRANSMIT_REG )
			{
				midiFIFO[ midiFIFOIdx++ ] = D;
				midiFIFOIdx &= 3;
				MC = midiFIFO[ ( 4 + midiFIFOIdx - 2 ) & 3 ] & 0xf0;
				if ( MC == 0xc0 /*|| MD == 0xd0*/) // program and channel pressure
				{
					MC = midiFIFO[ ( 4 + midiFIFOIdx - 2 ) & 3 ];
					MD1 = midiFIFO[ ( midiFIFOIdx + 4 - 1 ) & 3 ] & 127;
					MD2 = 0;
					ringBufGPIO[ ringWrite ] = (1<<31) | MC | ( MD1 << 8 ) | ( MD2 << 16 );
					ringTime[ ringWrite ] = cycleCountC64;
					ringWrite ++;
					ringWrite &= ( RING_SIZE - 1 );

					*(u32*)&midiFIFO[0] = 0;
				} else
				if ( MC == 0xd0 ) // channel pressure
				{
					*(u32*)&midiFIFO[0] = 0;
				} else
				{
					MC = midiFIFO[ ( 4 + midiFIFOIdx - 3 ) & 3 ] & 0xf0;
					if ( MC == 0x90 || MC == 0x80 || MC == 0xe0 || MC == 0xb0 ) // commands with two parameters
					{
						MC = midiFIFO[ ( 4 + midiFIFOIdx - 3 ) & 3 ];
						MD1 = midiFIFO[ ( midiFIFOIdx + 4 - 2 ) & 3 ] & 127;
						MD2 = midiFIFO[ ( midiFIFOIdx + 4 - 1 ) & 3 ] & 127;
						ringBufGPIO[ ringWrite ] = (1<<31) | MC | ( MD1 << 8 ) | ( MD2 << 16 );
						ringTime[ ringWrite ] = cycleCountC64;
						ringWrite ++;
						ringWrite &= ( RING_SIZE - 1 );
						*(u32*)&midiFIFO[0] = 0;
					}
				}
			} else
			{
				register u8 D = 0;
				// read from IO1
				if ( (A&3) == MIDI_STATUS_REG )
				{
					// available for write? always :-)
					D |= 1 << 1;

					// data ready for read? no
					//D |= 1 << 0;
					WRITE_D0to7_TO_BUS( D )
					FINISH_BUS_HANDLING
					return;
				} else 
				if ( (A&3) == MIDI_RECEIVE_REG )
				{
					D = 0;
					WRITE_D0to7_TO_BUS( D )
					FINISH_BUS_HANDLING
					return;
				}
			}
		}
	}
#endif


	//  ___                      ___    __                     ___    __  
	// |__   |\/| |  | |     /\   |  | /  \ |\ |    | |\ |    |__  | /  \ 
	// |___  |  | \__/ |___ /~~\  |  | \__/ | \|    | | \|    |    | \__X 
	// OPTIONAL and omitted for this release
	//																	
	#ifdef EMULATION_IN_FIQ
	run_emulation:
	#include "fragment_emulation_in_fiq.h"
	#endif		

	//  __                 __       ___  __       ___ 
	// |__) |  |  |\/|    /  \ |  |  |  |__) |  |  |  
	// |    |/\|  |  |    \__/ \__/  |  |    \__/  |  
	// OPTIONAL
	//											
	#ifdef USE_PWM_DIRECT
	if ( outputPWM )
	{
		static unsigned long long samplesElapsedBeforeFIQ = 0;

		unsigned long long samplesElapsedFIQ = ( ( unsigned long long )cycleCountC64 * ( unsigned long long )SAMPLERATE ) / ( unsigned long long )CLOCKFREQ;
		if ( samplesElapsedFIQ != samplesElapsedBeforeFIQ && !CPU_RESET )
		{
			write32( ARM_GPIO_GPCLR0, bCTRL257 ); 
			samplesElapsedBeforeFIQ = samplesElapsedFIQ;

			u32 s = getSample();
			u16 s1 = s & 65535;
			u16 s2 = s >> 16;

			s32 d1 = (s32)( ( *(s16*)&s1 + 32768 ) * PWMRange ) >> 17;
			s32 d2 = (s32)( ( *(s16*)&s2 + 32768 ) * PWMRange ) >> 17;
			write32( ARM_PWM_DAT1, d1 );
			write32( ARM_PWM_DAT2, d2 );
			RESET_CPU_CYCLE_COUNTER
			return;
		} 
	}
	#endif
	#ifdef HDMI_SOUND
	if ( outputHDMISound )
	{
		static unsigned long long samplesElapsedBeforeFIQ = 0;

		if ( first && nCyclesEmulated > 0 )
		{
			first = 0;
			samplesElapsedBeforeFIQ = 0;
		} 

		if ( !first )
		{
		//	unsigned long long samplesElapsedFIQ = ( ( unsigned long long )cycleCountC64 * ( unsigned long long )SAMPLERATE ) / ( unsigned long long )CLOCKFREQ;
			unsigned long long samplesElapsedFIQ = ( ( unsigned long long )cycleCountC64 * ( unsigned long long )48000 ) / ( unsigned long long )CLOCKFREQ;
			if ( samplesElapsedFIQ != samplesElapsedBeforeFIQ && !CPU_RESET )
			{
				write32( ARM_GPIO_GPCLR0, bCTRL257 ); 
				samplesElapsedBeforeFIQ = samplesElapsedFIQ;

				u32 s1, s2;
				getSampleHDMI( &s1, &s2 );
				if ( !( read32( RegMaiControl ) & BitMaiControlFull ) )
				{
					write32( RegMaiData, s1 );
					write32( RegMaiData, s2 );
				}

				RESET_CPU_CYCLE_COUNTER
				return;
			}
		}
	} 
	#endif
	//           ___  __       
	// |     /\   |  /  ` |__| 
	// |___ /~~\  |  \__, |  | 
	//
	#ifdef COMPILE_MENU
	#ifdef USE_LATCH_OUTPUT
	if ( screenType == 0 )
	{
		if ( --latchDelayOut == 1 && renderDone == 3 )
		{
			prefetchI2C();
		}
		if ( latchDelayOut <= 0 && renderDone == 3 )
		{
			latchDelayOut = 2;
			prepareOutputLatch();
			if ( bufferEmptyI2C() ) renderDone = 0;
			OUTPUT_LATCH_AND_FINISH_BUS_HANDLING
			return;

		}
	}
	#endif

	/*u32 swizzle = 
		( (fCount & 128) >> 7 ) |
		( (fCount & 64) >> 5 ) |
		( (fCount & 32) >> 3 ) |
		( (fCount & 16) >> 1 ) |
		( (fCount & 8) << 1 ) |
		( (fCount & 4) << 3 ) |
		( (fCount & 2) << 5 ) |
		( (fCount & 1) << 7 );*/
	#endif

	static u32 lastButtonPressed = 0;

	if ( lastButtonPressed > 0 )
		lastButtonPressed --;

	static u32 buttonIsPressed = 0;

	if ( BUTTON_PRESSED && lastButtonPressed == 0 )
		buttonIsPressed ++; else
		buttonIsPressed = 0;

	if ( buttonIsPressed > 50 )
	{
		visModeGotoNext = 1;
		vu_Mode = ( vu_Mode + 1 ) & 3;
		lastButtonPressed = 100000;
	}

	#ifdef COMPILE_MENU
	if ( screenType == 0 )
	{
		/*if ( vu_nLEDs != 0xffff )
		{
			if ( vu_Mode == 0 )
			{
				setLatchFIQ( LATCH_ON[ vu_nLEDs ] );
				clrLatchFIQ( LATCH_OFF[ vu_nLEDs ] );
			} else
			if ( vu_Mode == 1 )
			{
				if ( swizzle < vuMeter[ 0 ] )
					setLatchFIQ( LATCH_LED_ALL ); else
					clrLatchFIQ( LATCH_LED_ALL );		
			} else
			if ( vu_Mode == 2 )
			{
				u32 led =
					( ( swizzle < vuMeter[ 1 ] ) ? LATCH_LED1 : 0 ) |
					( ( swizzle < vuMeter[ 2 ] ) ? LATCH_LED2 : 0 ) |
					( ( swizzle < vuMeter[ 3 ] ) ? LATCH_LED3 : 0 );

				setLatchFIQ( led );
				clrLatchFIQ( ( (~led) & LATCH_LED_ALL ) | LATCH_LED0 );		
			} else
				clrLatchFIQ( LATCH_LED_ALL );		
		}*/
	} else
	{
		prepareOutputLatch4Bit();
		outputLatch();
	}
	#endif

	static u32 cycleCount = 0;
	if ( !((++cycleCount)&8191) )
		clrLatchFIQ( LATCH_LED0|LATCH_LED1 );

	OUTPUT_LATCH_AND_FINISH_BUS_HANDLING
}

#ifndef COMPILE_MENU
int main( void )
{
	CKernel kernel;
	if ( kernel.Initialize() )
		kernel.Run();

	halt();
	return EXIT_HALT;
}
#endif
