frntc/Sidekick64/Source/Firmware/STSoundLib/YmMusic.cpp

/*-----------------------------------------------------------------------------

	ST-Sound ( YM files player library )

	YM Music Driver

-----------------------------------------------------------------------------*/

/*-----------------------------------------------------------------------------
* ST-Sound, ATARI-ST Music Emulator
* Copyright (c) 1995-1999 Arnaud Carre ( http://leonard.oxg.free.fr )
* All rights reserved.
*
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
-----------------------------------------------------------------------------*/

#include <string.h>
#include <stdlib.h>
#include <assert.h>
#include "YmMusic.h"

#define	_LINEAR_OVRS				// Activate linear oversampling (best quality) Only used for DigiMix and UniversalTracker YM file type


// ATARI-ST MFP chip predivisor
static	const ymint	mfpPrediv[8] = {0,4,10,16,50,64,100,200};



CYmMusic::CYmMusic(ymint _replayRate) :
    ymChip(ATARI_CLOCK, 1, _replayRate)
{
	pBigMalloc = NULL;
	pSongName = NULL;
	pSongAuthor = NULL;
	pSongComment = NULL;
	pSongType = NULL;
	pSongPlayer = NULL;

	pBigSampleBuffer = NULL;
	pMixBlock = NULL;

	replayRate = _replayRate;
	innerSamplePos = 0;
	currentPos = 0;
	nbDrum = 0;
	pDrumTab = NULL;
	setLoopMode(YMFALSE);

	m_pTimeInfo = NULL;
}

void	CYmMusic::setTimeControl(ymbool bTime)
{
		if (bTime)
			attrib |= A_TIMECONTROL;
		else
			attrib &= (~A_TIMECONTROL);
}

CYmMusic::~CYmMusic()
{
		stop();
		unLoad();
}

void	CYmMusic::setLoopMode(ymbool bLoopMode)
{
		bLoop = bLoopMode;
}

void	CYmMusic::setPlayerRate(ymint rate)
{
		playerRate = rate;
}

ymu32 CYmMusic::getPos()
{
	if ((songType>=YM_MIX1) && (songType<YM_MIXMAX))
	{
		// avoid overflow after 97 seconds and keep only 32bit computing
		return m_iMusicPosInMs;
	}
	else if ((nbFrame>0) && (playerRate>0))
	{
		return ((ymu32)currentFrame*1000)/(ymu32)playerRate;
	}
	else
		return 0;

}

ymu32	CYmMusic::getMusicTime(void)
{

	if ((songType>=YM_MIX1) && (songType<YM_MIXMAX))
	{
		return m_musicLenInMs;
	}
	else if ((nbFrame>0) && (playerRate>0))
	{
		return ((ymu32)nbFrame*1000)/(ymu32)playerRate;
	}
	else
		return 0;

}


void	CYmMusic::setMixTime(ymu32 time)
{
	if (time > m_musicLenInMs)
		return;

	assert(m_pTimeInfo);
	for (int i=0;i<m_nbTimeKey;i++)
	{
		ymu32 tEnd = i < (m_nbTimeKey-1) ? m_pTimeInfo[i+1].time : m_musicLenInMs;
		if ((time >= m_pTimeInfo[i].time) && (time < tEnd))
		{
			mixPos = m_pTimeInfo[i].nBlock;
			pCurrentMixSample = pBigSampleBuffer + pMixBlock[mixPos].sampleStart;
			currentSampleLength = (pMixBlock[mixPos].sampleLength)<<12;
			currentPente = (((ymu32)pMixBlock[mixPos].replayFreq)<<12) / replayRate;

			ymu32 len = tEnd - m_pTimeInfo[i].time;
			ymu32 t0 = ((time - m_pTimeInfo[i].time) * pMixBlock[mixPos].sampleLength) / len;

			currentPos = t0 << 12;
			nbRepeat = m_pTimeInfo[i].nRepeat;
			break;
		}
	}

	m_iMusicPosInMs = time;
	m_iMusicPosAccurateSample = 0;
}

ymu32	CYmMusic::setMusicTime(ymu32 time)
{
		if (!isSeekable()) return 0;
		ymu32 newTime = 0;

		if ((songType>=YM_V2) && (songType<YM_VMAX))
		{
			newTime = time;
			if (newTime>=getMusicTime()) newTime = 0;
			currentFrame = (newTime*(ymu32)playerRate)/1000;
		}
		else if ((songType>=YM_TRACKER1) && (songType<YM_TRACKERMAX))
		{
			newTime = time;
			if (newTime>=getMusicTime()) newTime = 0;
			currentFrame = (newTime*(ymu32)playerRate)/1000;
		}
		else if ((songType>=YM_MIX1) && (songType<YM_MIXMAX))
		{
			assert(m_pTimeInfo);
			setMixTime(time);
		}

		return newTime;
}

void	CYmMusic::restart(void)
{
	setMusicTime(0);
	bMusicOver = YMFALSE;
}



void	CYmMusic::getMusicInfo(ymMusicInfo_t *pInfo)
{
		if (pInfo)
		{
			pInfo->pSongName = pSongName;
			pInfo->pSongAuthor = pSongAuthor;
			pInfo->pSongComment = pSongComment;
			pInfo->pSongType = pSongType;
			pInfo->pSongPlayer = pSongPlayer;

			pInfo->musicTimeInMs = getMusicTime();
			pInfo->musicTimeInSec = pInfo->musicTimeInMs / 1000;
		}
}


void	CYmMusic::setAttrib(ymint _attrib)
{
		attrib = _attrib;
}

ymint		CYmMusic::getAttrib(void)
{
		return attrib;
}

ymbool	CYmMusic::isSeekable(void)
{
		return getAttrib()&A_TIMECONTROL;
}

void	CYmMusic::setLastError(const char *pError)
{
		pLastError = pError;
}

const char	*CYmMusic::getLastError(void)
{
		return pLastError;
}

void	bufferClear(ymsample *pBuffer,ymint nbSample)
{
		memset((void*)pBuffer,0,nbSample*sizeof(ymsample));
}

ymbool	CYmMusic::update(ymsample *sampleBuffer,ymint nbSample)
{
ymint sampleToCompute;
ymint	vblNbSample;


		if ((!bMusicOk) ||
			(bPause) ||
			(bMusicOver))
		{
			bufferClear(sampleBuffer,nbSample);
			if (bMusicOver)
				return YMFALSE;
			else
				return YMTRUE;
		}

		if ((songType >= YM_MIX1) && (songType < YM_MIXMAX))
		{
			stDigitMix(sampleBuffer,nbSample);


		}
		else if ((songType >= YM_TRACKER1) && (songType<YM_TRACKERMAX))
		{
			ymTrackerUpdate(sampleBuffer,nbSample);
		}
		else
		{
			ymsample *pOut = sampleBuffer;
			ymint nbs = nbSample;
			vblNbSample = replayRate/playerRate;
			do
			{
				// Nb de sample à calculer avant l'appel de Player
				sampleToCompute = vblNbSample-innerSamplePos;
				// Test si la fin du buffer arrive avant la fin de sampleToCompute
				if (sampleToCompute>nbs) sampleToCompute = nbs;
				innerSamplePos += sampleToCompute;
				if (innerSamplePos>=vblNbSample)
				{
					player();			// Lecture de la partition (playerRate Hz)
					innerSamplePos -= vblNbSample;
				}
				if (sampleToCompute>0)
				{
					ymChip.update(pOut,sampleToCompute);	// YM Emulation.
					pOut += sampleToCompute;
				}
				nbs -= sampleToCompute;
			}
			while (nbs>0);
		}


		return YMTRUE;
}
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
